KitSprout/SmartIMU/firmware/NRF_Peripheral_RADIO/Program/drivers/nrf5x_system.h

/**
 *      __            ____
 *     / /__ _  __   / __/                      __  
 *    / //_/(_)/ /_ / /  ___   ____ ___  __ __ / /_ 
 *   / ,<  / // __/_\ \ / _ \ / __// _ \/ // // __/ 
 *  /_/|_|/_/ \__//___// .__//_/   \___/\_,_/ \__/  
 *                    /_/   github.com/KitSprout    
 * 
 *  @file    nrf5x_system.h
 *  @author  KitSprout
 *  @date    21-Apr-2018
 *  @brief   
 * 
 */

/* Define to prevent recursive inclusion ---------------------------------------------------*/
#ifndef __NRF5x_SYSTEM_H
#define __NRF5x_SYSTEM_H

#ifdef __cplusplus
  extern "C" {
#endif

/* Includes --------------------------------------------------------------------------------*/
#include "nrf.h"
#include "nrf5x_conf.h"
#include "nrf5x_delay.h"
#include "algorithms\mathUnit.h"
#include "boardConfig.h"

/* Define ----------------------------------------------------------------------------------*/
/* Macro -----------------------------------------------------------------------------------*/
#define NRF5x_SYSCLK                        SystemCoreClock
#define NRF5x_UUID()                        ((uint64_t)(((uint64_t)NRF_FICR->DEVICEID[1] << 32) |  NRF_FICR->DEVICEID[0]))

#define __GPIO_SET(__PORT, __PIN)           ((__PORT)->OUTSET = 1UL << (__PIN))
#define __GPIO_RST(__PORT, __PIN)           ((__PORT)->OUTCLR = 1UL << (__PIN))
#define __GPIO_TOG(__PORT, __PIN)           ((__PORT)->OUT ^= 1UL << (__PIN))
#define __GPIO_READ(__PORT, __PIN)          (((__PORT)->IN >> (__PIN)) & 1UL)

#define BYTE32(__BH2, __BH1, __BL2, __BL1)  (((uint8_t)(__BH2)<<24U) | ((uint8_t)(__BH1)<<16U) | ((uint8_t)(__BL2)<<8U)  | ((uint8_t)(__BL1)))
#define BYTE32U16H(__B32U16)                ((uint16_t)(((uint32_t)(__B32U16)&0xFFFF0000)>>16U))
#define BYTE32U16L(__B32U16)                ((uint16_t)( (uint32_t)(__B32U16)&0x0000FFFF))
#define BYTE32U8_4(__B32U8)                 ((uint8_t)(((uint32_t)(__B32U8)&0xFF000000)>>24U))
#define BYTE32U8_3(__B32U8)                 ((uint8_t)(((uint32_t)(__B32U8)&0x00FF0000)>>16U))
#define BYTE32U8_2(__B32U8)                 ((uint8_t)(((uint32_t)(__B32U8)&0x0000FF00)>>8U))
#define BYTE32U8_1(__B32U8)                 ((uint8_t)( (uint32_t)(__B32U8)&0x000000FF))

#define BYTE16(__BH, __BL)                  ((((uint16_t)(__BH))<<8U) | ((uint16_t)(__BL)))
#define BYTE16U8H(__B16U8)                  ((uint8_t)(((uint16_t)(__B16U8)&0xFF00)>>8U))
#define BYTE16U8L(__B16U8)                  ((uint8_t)( (uint16_t)(__B16U8)&0x00FF))


/* Typedef ---------------------------------------------------------------------------------*/
typedef void (*pFunc)( void );

typedef enum {
  KS_OK       = 0U,
  KS_ERROR    = 1U,
  KS_BUSY     = 2U,
  KS_TIMEOUT  = 3U
} KS_StatusTypeDef;

typedef enum {
  RESET = 0U, 
  SET = !RESET
} FlagStatus;

typedef enum {
  DISABLE = 0U, 
  ENABLE = !DISABLE
} FunctionalState;

/* Extern ----------------------------------------------------------------------------------*/
/* Functions -------------------------------------------------------------------------------*/

#ifdef __cplusplus
}
#endif

#endif

/*************************************** END OF FILE ****************************************/
