KitSprout/SmartIMU/firmware/NRF_Peripheral_RADIO/Program/modules/kSerial.h

/**
 *      __            ____
 *     / /__ _  __   / __/                      __  
 *    / //_/(_)/ /_ / /  ___   ____ ___  __ __ / /_ 
 *   / ,<  / // __/_\ \ / _ \ / __// _ \/ // // __/ 
 *  /_/|_|/_/ \__//___// .__//_/   \___/\_,_/ \__/  
 *                    /_/   github.com/KitSprout    
 * 
 *  @file    kSerial.h
 *  @author  KitSprout
 *  @date    22-Apr-2018
 *  @brief   
 * 
 */

/* Define to prevent recursive inclusion ---------------------------------------------------*/
#ifndef __KSERIAL_H
#define __KSERIAL_H

#ifdef __cplusplus
  extern "C" {
#endif

/* Includes --------------------------------------------------------------------------------*/
#include "drivers\nrf5x_system.h"
#include "algorithms\mathUnit.h"

/* Define ----------------------------------------------------------------------------------*/
#define KSERIAL_SEND_ENABLE   (1U)
#define KSERIAL_RECV_ENABLE   (1U)

/* Macro -----------------------------------------------------------------------------------*/
/* Typedef ---------------------------------------------------------------------------------*/
/* Extern ----------------------------------------------------------------------------------*/
/* Functions -------------------------------------------------------------------------------*/
void      kSerial_SetSendFunction( uint32_t (*fptr)(uint8_t *, uint32_t) );
void      kSerial_SetRecvByteFunction( uint8_t (*fptr)(void) );

uint32_t  kSerial_Check( uint8_t *packet, void *param, uint16_t *lens, uint8_t *type );
uint32_t  kSerial_Pack( uint8_t *packet, void *param, void *data, const uint16_t lens, const uint8_t type );
uint32_t  kSerial_Unpack( uint8_t *packet, void *param, void *data, uint16_t *lens, uint8_t *type );
uint32_t  kSerial_SendPacket( void *param, void *data, const uint16_t lens, const uint8_t type );
uint32_t  kSerial_RecvPacket( void *param, void *data, uint16_t *lens, uint8_t *type );
uint16_t  kSerial_GetPacketDataLens( uint16_t lens, uint8_t type );

#ifdef __cplusplus
}
#endif

#endif

/*************************************** END OF FILE ****************************************/
