KitSprout/SmartIMU/firmware/NRF_Peripheral_RADIO/Program/nrf5x_conf.h

/**
 *      __            ____
 *     / /__ _  __   / __/                      __  
 *    / //_/(_)/ /_ / /  ___   ____ ___  __ __ / /_ 
 *   / ,<  / // __/_\ \ / _ \ / __// _ \/ // // __/ 
 *  /_/|_|/_/ \__//___// .__//_/   \___/\_,_/ \__/  
 *                    /_/   github.com/KitSprout    
 * 
 *  @file    nrf5x_conf.h
 *  @author  KitSprout
 *  @date    16-Jun-2018
 *  @brief   
 * 
 */

/* Define to prevent recursive inclusion ---------------------------------------------------*/
#ifndef __NRF5x_CONF_H
#define __NRF5x_CONF_H

#ifdef __cplusplus
  extern "C" {
#endif

/* Includes --------------------------------------------------------------------------------*/

//#include "nrf_adc.h"      // ADC
#include "nrf_clock.h"    // CLOCK
//#include "nrf_comp.h"     // COMP
//#include "nrf_delay.h"    // DELAY
//#include "nrf_ecb.h"      // ECB
//#include "nrf_egu.h"      // EGU
//#include "nrf_error.h"    // ERROR
#include "nrf_gpio.h"     // GPIO
//#include "nrf_gpiote.h"   // GPIOTE
//#include "nrf_i2s.h"      // I2S
//#include "nrf_lpcomp.h"   // LPCOMP
//#include "nrf_nvic.h"     // NVIC
//#include "nrf_nvmc.h"     // NVMC
//#include "nrf_pdm"        // PDM
//#include "nrf_power"      // POWER
//#include "nrf_ppi.h"      // PPI
//#include "nrf_pwm.h"      // PWM
//#include "nrf_qdec.h"     // QDEC
//#include "nrf_qspi.h"     // QSPI
//#include "nrf_rng.h"      // RNG
//#include "nrf_rtc.h"      // RTC
//#include "nrf_saadc.h"    // SAADC
//#include "nrf_soc.h"      // SOC
//#include "nrf_spi.h"      // SPI
//#include "nrf_spim.h"     // SPIM
//#include "nrf_spis.h"     // SPIS
//#include "nrf_systick.h"  // SYSTICK
//#include "nrf_temp.h"     // TEMP
#include "nrf_timer.h"    // TIMER
//#include "nrf_twi.h"      // TWI
//#include "nrf_twim.h"     // TWIM
//#include "nrf_twis.h"     // TWIS
//#include "nrf_uart.h"     // UART
#include "nrf_uarte.h"    // UARTE
//#include "nrf_usbd.h"     // USBD
//#include "nrf_wdt.h"      // WDT

/* Define ----------------------------------------------------------------------------------*/
/* Macro -----------------------------------------------------------------------------------*/
/* Typedef ---------------------------------------------------------------------------------*/
/* Extern ----------------------------------------------------------------------------------*/
/* Functions -------------------------------------------------------------------------------*/

#ifdef __cplusplus
}
#endif

#endif

/*************************************** END OF FILE ****************************************/
