KitSprout/SmartIMU/Software/SIMU_Peripheral_EXTI/Program/smartimu_it.c

/**
  *      __            ____
  *     / /__ _  __   / __/                      __  
  *    / //_/(_)/ /_ / /  ___   ____ ___  __ __ / /_ 
  *   / ,<  / // __/_\ \ / _ \ / __// _ \/ // // __/ 
  *  /_/|_|/_/ \__//___// .__//_/   \___/\_,_/ \__/  
  *                    /_/   github.com/KitSprout    
  * 
  * @file    smartimu_it.c
  * @author  KitSprout
  * @date    5-Nov-2016
  * @brief   
  * 
  */

/* Includes --------------------------------------------------------------------------------*/
#include "drivers\stm32f4_system.h"
#include "drivers\stm32f4_exti.h"

/** @addtogroup STM32_Interrupt
  * @{
  */

/* Private variables -----------------------------------------------------------------------*/
/* Private functions -----------------------------------------------------------------------*/

void NMI_Handler( void ) { while(1); }
void HardFault_Handler( void ) { while(1); }
void MemManage_Handler( void ) { while(1); }
void BusFault_Handler( void ) { while(1); }
void UsageFault_Handler( void ) { while(1); }
void SVC_Handler( void ) {}
void DebugMon_Handler( void ) {}
void PendSV_Handler( void ) {}
void SysTick_Handler( void ) { HAL_IncTick(); }

//void WWDG_IRQHandler( void )
//void PVD_IRQHandler( void )
//void TAMP_STAMP_IRQHandler( void )
//void RTC_WKUP_IRQHandler( void )
//void FLASH_IRQHandler( void )
//void RCC_IRQHandler( void )
void EXTI0_IRQHandler( void )
{
  HAL_GPIO_EXTI_IRQHandler(EXTI0_PIN);
}
//void EXTI1_IRQHandler( void )
//void EXTI2_IRQHandler( void )
//void EXTI3_IRQHandler( void )
//void EXTI4_IRQHandler( void )
//void DMA1_Stream0_IRQHandler( void )
//void DMA1_Stream1_IRQHandler( void )
//void DMA1_Stream2_IRQHandler( void )
//void DMA1_Stream3_IRQHandler( void )
//void DMA1_Stream4_IRQHandler( void )
//void DMA1_Stream5_IRQHandler( void )
//void DMA1_Stream6_IRQHandler( void )
//void ADC_IRQHandler( void )
//void CAN1_TX_IRQHandler( void )
//void CAN1_RX0_IRQHandler( void )
//void CAN1_RX1_IRQHandler( void )
//void CAN1_SCE_IRQHandler( void )
//void EXTI9_5_IRQHandler( void )
//void TIM1_BRK_TIM9_IRQHandler( void )
//void TIM1_UP_TIM10_IRQHandler( void )
//void TIM1_TRG_COM_TIM11_IRQHandler( void )
//void TIM1_CC_IRQHandler( void )
//void TIM2_IRQHandler( void )
//void TIM3_IRQHandler( void )
//void TIM4_IRQHandler( void )
//void I2C1_EV_IRQHandler( void )
//void I2C1_ER_IRQHandler( void )
//void I2C2_EV_IRQHandler( void )
//void I2C2_ER_IRQHandler( void )
//void SPI1_IRQHandler( void )
//void SPI2_IRQHandler( void )
//void USART1_IRQHandler( void )
//void USART2_IRQHandler( void )
//void USART3_IRQHandler( void )
//void EXTI15_10_IRQHandler( void )
//void RTC_Alarm_IRQHandler( void )
//void OTG_FS_WKUP_IRQHandler( void )
//void TIM8_BRK_TIM12_IRQHandler( void )
//void TIM8_UP_TIM13_IRQHandler( void )
//void TIM8_TRG_COM_TIM14_IRQHandler( void )
//void TIM8_CC_IRQHandler( void )
//void DMA1_Stream7_IRQHandler( void )
//void SDIO_IRQHandler( void )
//void TIM5_IRQHandler( void )
//void SPI3_IRQHandler( void )
//void TIM6_IRQHandler( void )
//void TIM7_IRQHandler( void )
//void DMA2_Stream0_IRQHandler( void )
//void DMA2_Stream1_IRQHandler( void )
//void DMA2_Stream2_IRQHandler( void )
//void DMA2_Stream3_IRQHandler( void )
//void DMA2_Stream4_IRQHandler( void )
//void DFSDM1_FLT0_IRQHandler( void )
//void DFSDM1_FLT1_IRQHandler( void )
//void CAN2_TX_IRQHandler( void )
//void CAN2_RX0_IRQHandler( void )
//void CAN2_RX1_IRQHandler( void )
//void CAN2_SCE_IRQHandler( void )
//void OTG_FS_IRQHandler( void )
//void DMA2_Stream5_IRQHandler( void )
//void DMA2_Stream6_IRQHandler( void )
//void DMA2_Stream7_IRQHandler( void )
//void USART6_IRQHandler( void )
//void I2C3_EV_IRQHandler( void )
//void I2C3_ER_IRQHandler( void )
//void RNG_IRQHandler( void )
//void FPU_IRQHandler( void )
//void SPI4_IRQHandler( void )
//void SPI5_IRQHandler( void )
//void QUADSPI_IRQHandler( void )
//void FMPI2C1_EV_IRQHandler( void )
//void FMPI2C1_ER_IRQHandler( void )

/*************************************** END OF FILE ****************************************/
